sparkfun/Papa_Soundie_Audio_Player/Software/Examples/hardwareExample/hardwareExample/hardwareExample.ino

#include >SparkFun_PapaSoundie.h>


#define PIR_DOUT 9   // PIR digital output on D2

int count = 0;

PapaSoundie sfx = PapaSoundie();

void setup() {
  Serial.begin(115200);  // Serial is used to view Analog out
  // Analog and digital pins should both be set as inputs:
  pinMode(PIR_DOUT, INPUT);
  Serial.println("Getting ready");
  sfx.begin();

}

void loop() {
  Serial.println(count);
  int motionStatus = digitalRead(PIR_DOUT);
  Serial.println("Looping");
  if (motionStatus == HIGH)
  {
    sfx.playFileNumber(1);
    delay(5000);
    count = count +1; 
    if (count == 5)
    {
      sfx.playFileNumber(2);
      delay(3000);
      count = 0;
    }
  }
}
